janelia-experimental-technology/FED3-RFID/ELECTRONICS/PHOTOS/20240327_181024.jpg

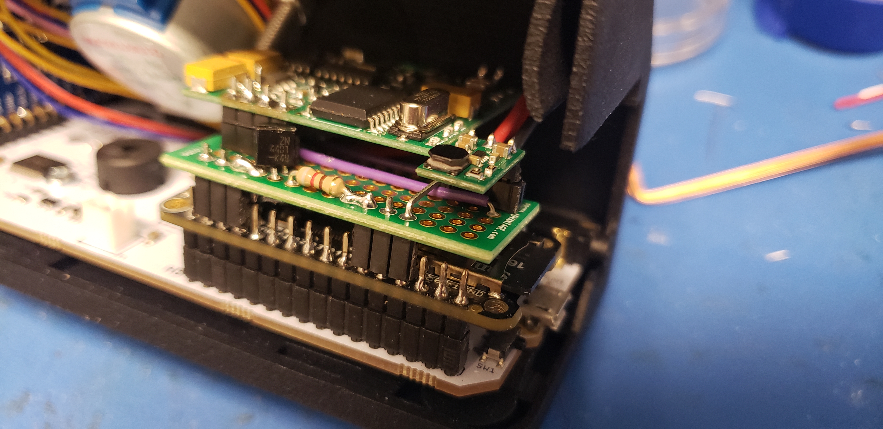
ELECTRONICS/PHOTOS/20240327_181024.jpg
