janelia-experimental-technology/FED3-RFID/ELECTRONICS/PHOTOS/20240327_181121.jpg

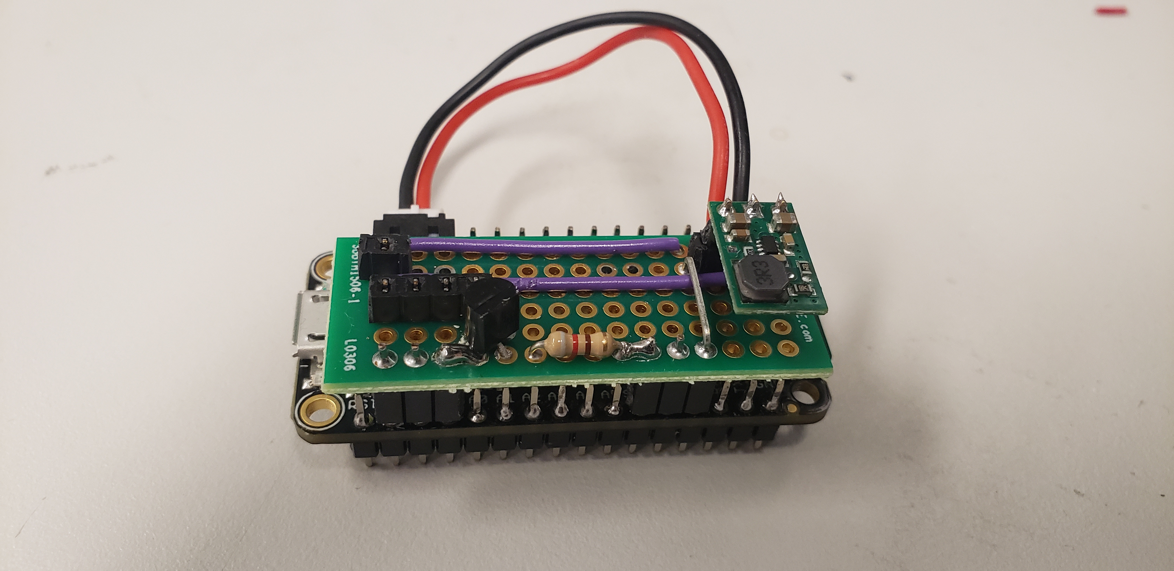
ELECTRONICS/PHOTOS/20240327_181121.jpg
