janelia-experimental-technology/FED3-RFID/FIRMWARE/FED3_support_libraries/Adafruit_AHTX0/assets/board.png

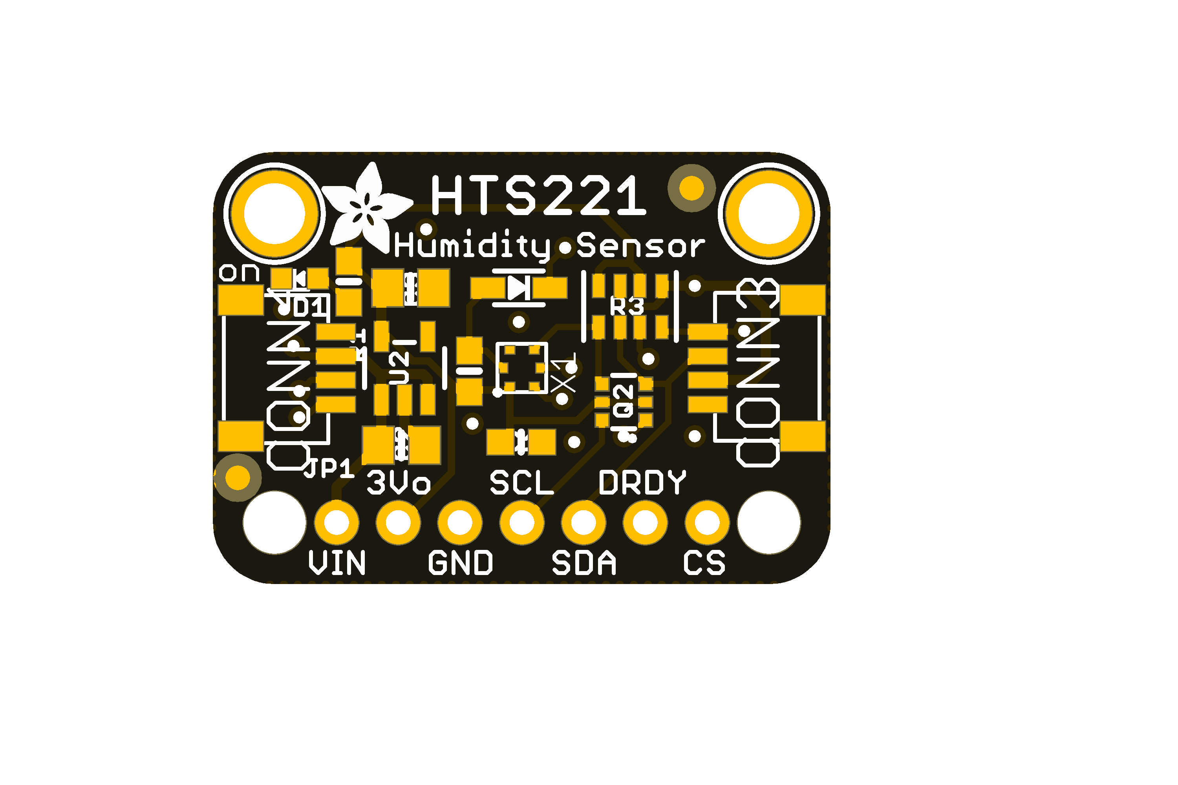
FIRMWARE/FED3_support_libraries/Adafruit_AHTX0/assets/board.png
