janelia-experimental-technology/FED3-RFID/FIRMWARE/FED3_support_libraries/SdFat/extras/AnalogBinLoggerExtras/ADC_ENOB.PNG

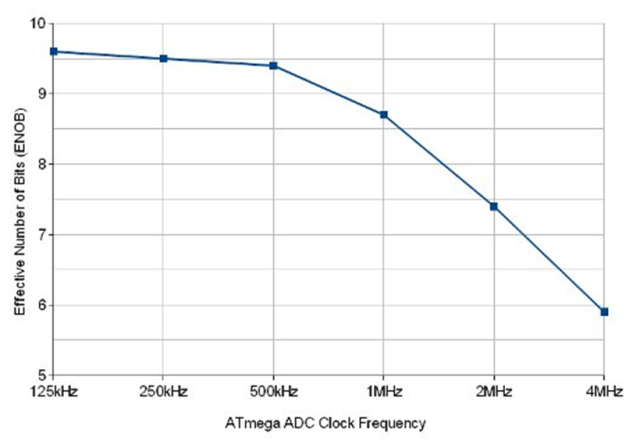
FIRMWARE/FED3_support_libraries/SdFat/extras/AnalogBinLoggerExtras/ADC_ENOB.PNG
