janelia-experimental-technology/FED3-RFID/FIRMWARE/FED3_support_libraries/SdFat/extras/AnalogBinLoggerExtras/DATA.png

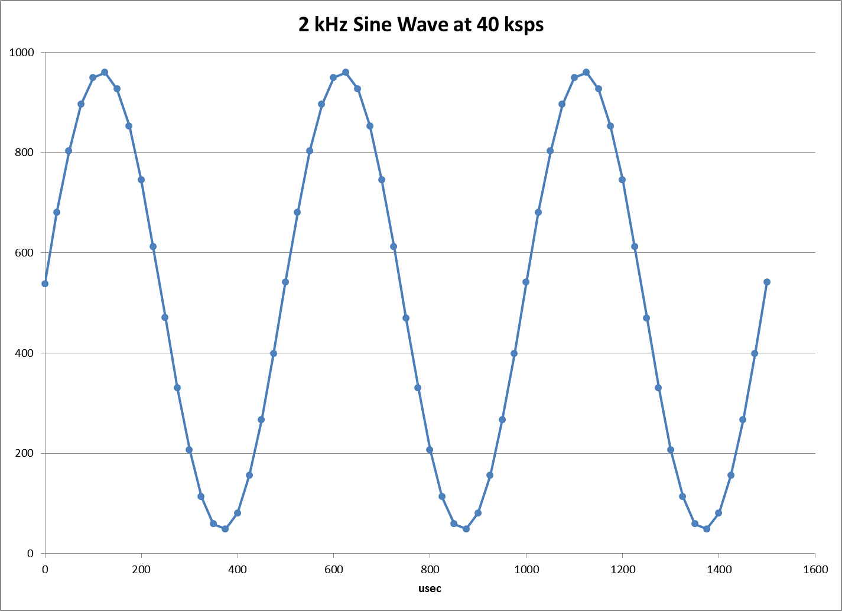
FIRMWARE/FED3_support_libraries/SdFat/extras/AnalogBinLoggerExtras/DATA.png
