janelia-experimental-technology/FED3-RFID/FIRMWARE/FED3_support_libraries/SdFat/extras/html/_fat_file_8h__incl.png

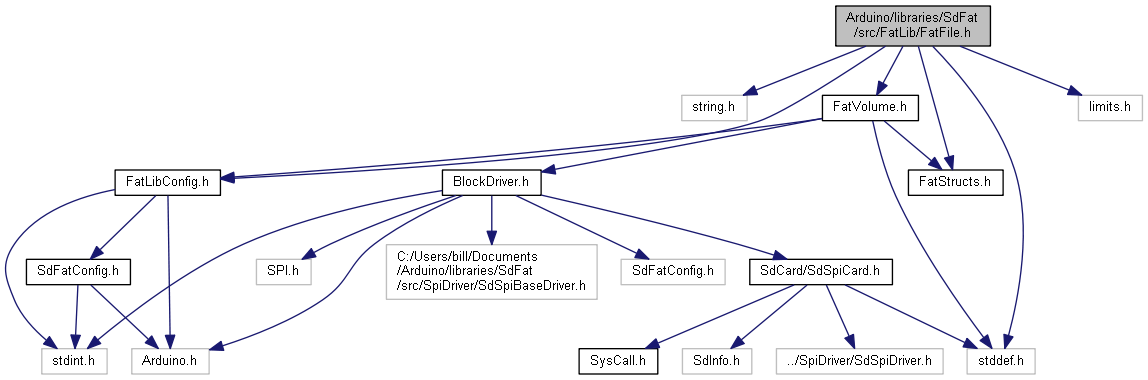
FIRMWARE/FED3_support_libraries/SdFat/extras/html/_fat_file_8h__incl.png
