janelia-experimental-technology/FED3-RFID/FIRMWARE/FED3_support_libraries/SdFat/extras/html/_sd_fat_8h__incl.png

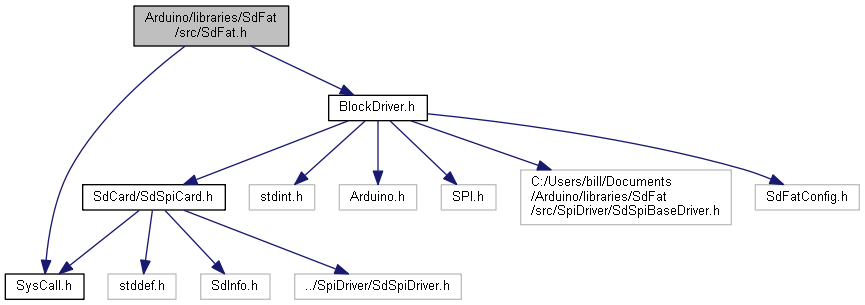
FIRMWARE/FED3_support_libraries/SdFat/extras/html/_sd_fat_8h__incl.png
