janelia-experimental-technology/FED3-RFID/FIRMWARE/FED3_support_libraries/SdFat/extras/html/_sys_call_8h__dep__incl.png

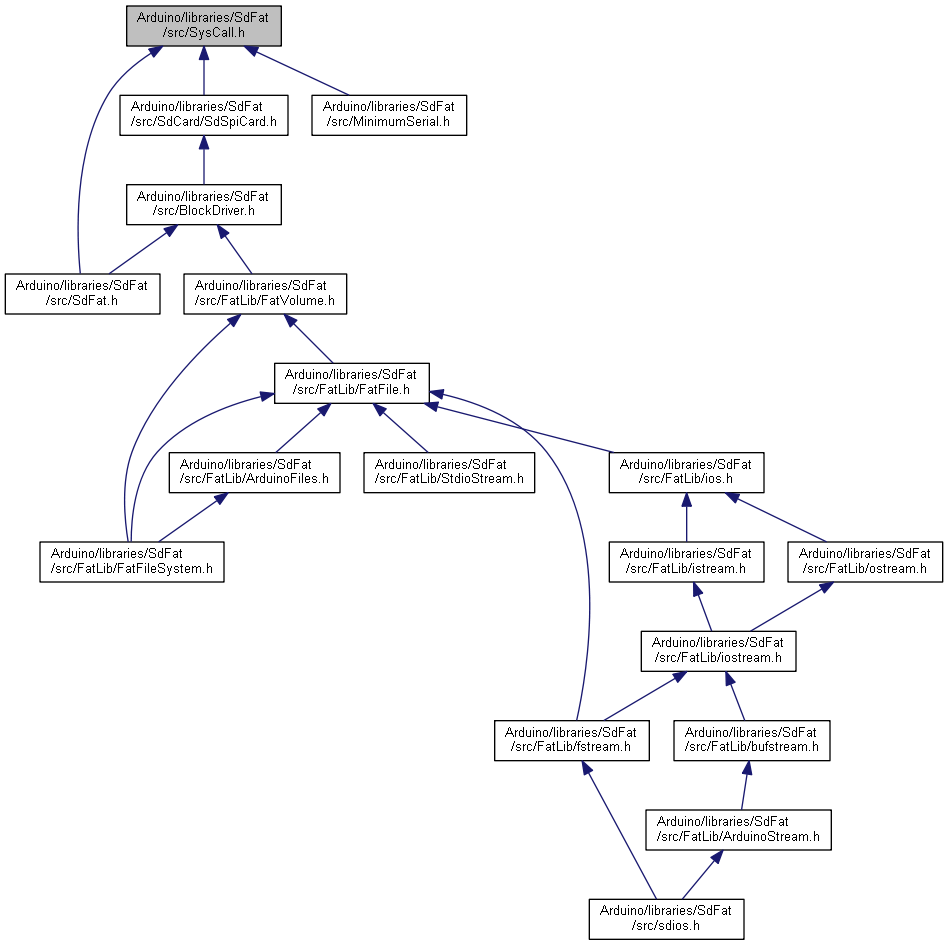
FIRMWARE/FED3_support_libraries/SdFat/extras/html/_sys_call_8h__dep__incl.png
