janelia-experimental-technology/FED3-RFID/FIRMWARE/FED3_support_libraries/SdFat/extras/html/class_arduino_in_stream__coll__graph.png

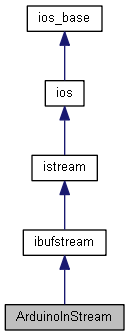
FIRMWARE/FED3_support_libraries/SdFat/extras/html/class_arduino_in_stream__coll__graph.png
