janelia-experimental-technology/FED3-RFID/FIRMWARE/FED3_support_libraries/SdFat/extras/html/class_base_block_driver__inherit__graph.png

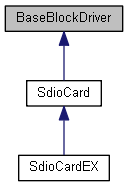
FIRMWARE/FED3_support_libraries/SdFat/extras/html/class_base_block_driver__inherit__graph.png
