janelia-experimental-technology/FED3-RFID/FIRMWARE/FED3_support_libraries/SdFat/extras/html/class_fat_file__inherit__graph.png

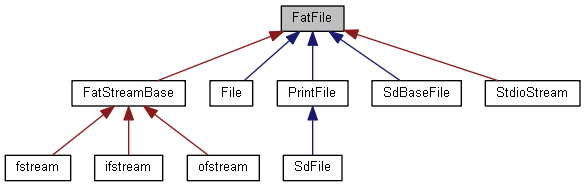
FIRMWARE/FED3_support_libraries/SdFat/extras/html/class_fat_file__inherit__graph.png
