janelia-experimental-technology/FED3-RFID/FIRMWARE/FED3_support_libraries/SdFat/extras/html/class_fat_stream_base__inherit__graph.png

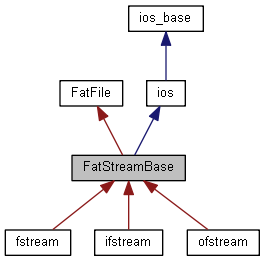
FIRMWARE/FED3_support_libraries/SdFat/extras/html/class_fat_stream_base__inherit__graph.png
