janelia-experimental-technology/FED3-RFID/FIRMWARE/FED3_support_libraries/SdFat/extras/html/class_sd_fat_sdio__coll__graph.png

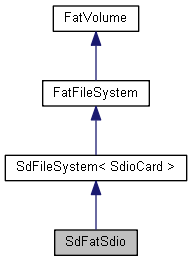
FIRMWARE/FED3_support_libraries/SdFat/extras/html/class_sd_fat_sdio__coll__graph.png
