janelia-experimental-technology/FED3-RFID/FIRMWARE/FED3_support_libraries/SdFat/extras/html/classfstream__coll__graph.png

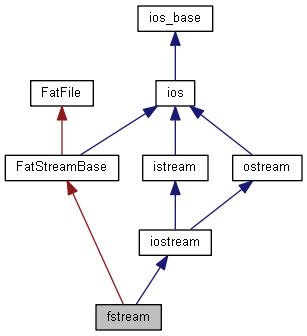
FIRMWARE/FED3_support_libraries/SdFat/extras/html/classfstream__coll__graph.png
