janelia-experimental-technology/FED3-RFID/FIRMWARE/FED3_support_libraries/SdFat/extras/html/dir_7e472674a7b7d2590a789f197241f95f_dep.png

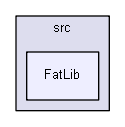
FIRMWARE/FED3_support_libraries/SdFat/extras/html/dir_7e472674a7b7d2590a789f197241f95f_dep.png
