janelia-experimental-technology/FED3-RFID/FIRMWARE/FED3_support_libraries/SdFat/extras/html/dir_481cc946b8a81b8d9363a4aad6201160_dep.png

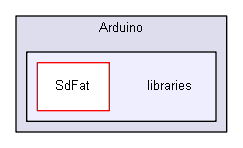
FIRMWARE/FED3_support_libraries/SdFat/extras/html/dir_481cc946b8a81b8d9363a4aad6201160_dep.png
