janelia-experimental-technology/FED3-RFID/FIRMWARE/FED3_support_libraries/SdFat/extras/html/dir_1281b15c327061056ab3b326e90c50cf_dep.png

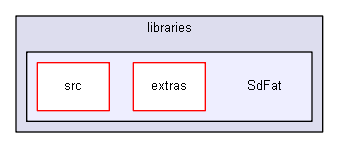
FIRMWARE/FED3_support_libraries/SdFat/extras/html/dir_1281b15c327061056ab3b326e90c50cf_dep.png
