janelia-experimental-technology/FED3-RFID/FIRMWARE/FED3_support_libraries/SdFat/extras/html/dir_c18d6c86f7b0afecac5c3a8a9885031e_dep.png

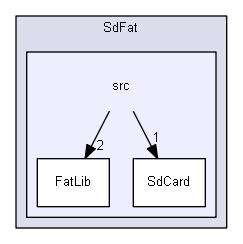
FIRMWARE/FED3_support_libraries/SdFat/extras/html/dir_c18d6c86f7b0afecac5c3a8a9885031e_dep.png
