janelia-experimental-technology/FED3-RFID/FIRMWARE/FED3_support_libraries/SdFat/extras/html/graph_legend.png

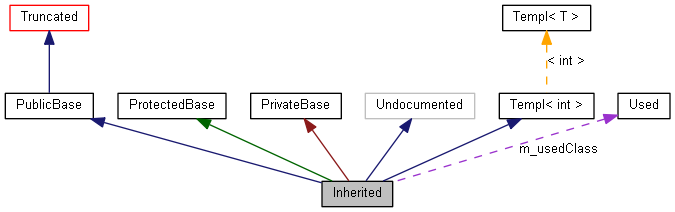
FIRMWARE/FED3_support_libraries/SdFat/extras/html/graph_legend.png
