janelia-experimental-technology/FED3-RFID/FIRMWARE/FED3_support_libraries/SdFat/extras/html/inherit_graph_10.png

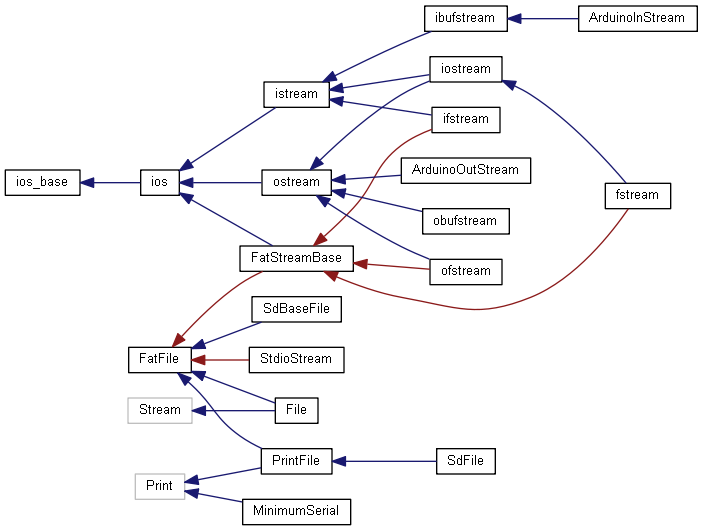
FIRMWARE/FED3_support_libraries/SdFat/extras/html/inherit_graph_10.png
