janelia-experimental-technology/FED3-RFID/FIRMWARE/FED3_support_libraries/SdFat/extras/html/structmaster_boot_record__coll__graph.png

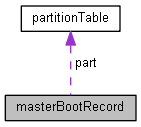
FIRMWARE/FED3_support_libraries/SdFat/extras/html/structmaster_boot_record__coll__graph.png
