janelia-experimental-technology/FED3-RFID/FIRMWARE/FED3_support_libraries/SdFat/extras/html/unioncache__t__coll__graph.png

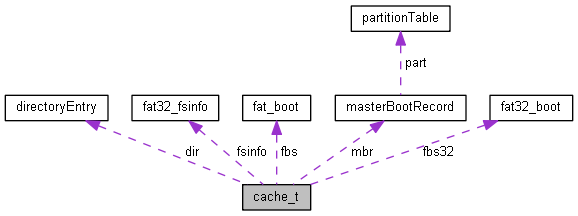
FIRMWARE/FED3_support_libraries/SdFat/extras/html/unioncache__t__coll__graph.png
