janelia-experimental-technology/FED3-RFID/RFID_HOUSING/PHOTOS/20240402_163826.jpg

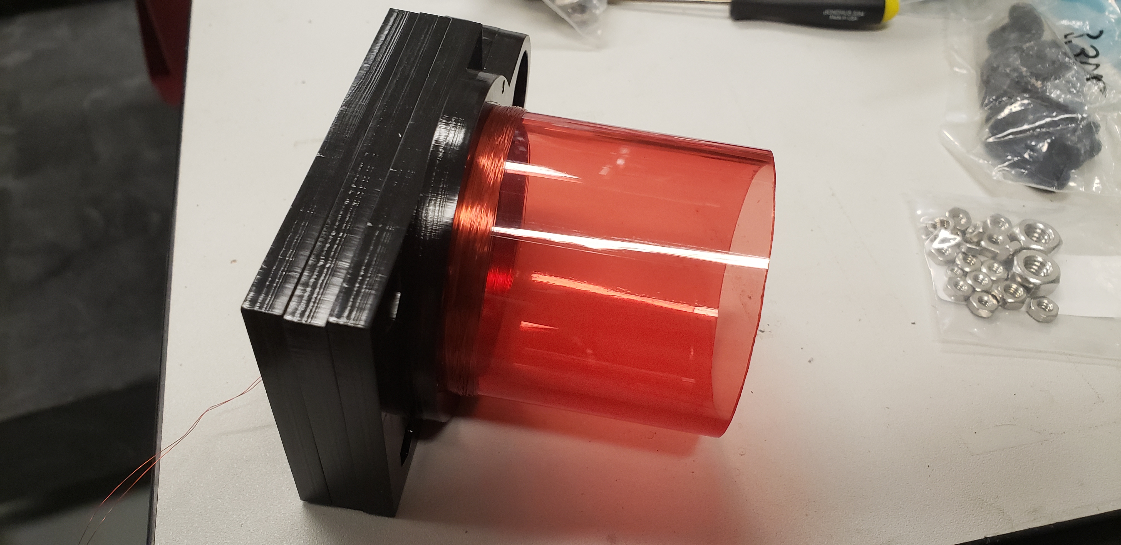
RFID_HOUSING/PHOTOS/20240402_163826.jpg
