janelia-experimental-technology/FED3-RFID/RFID_HOUSING/PHOTOS/20240402_172739.jpg

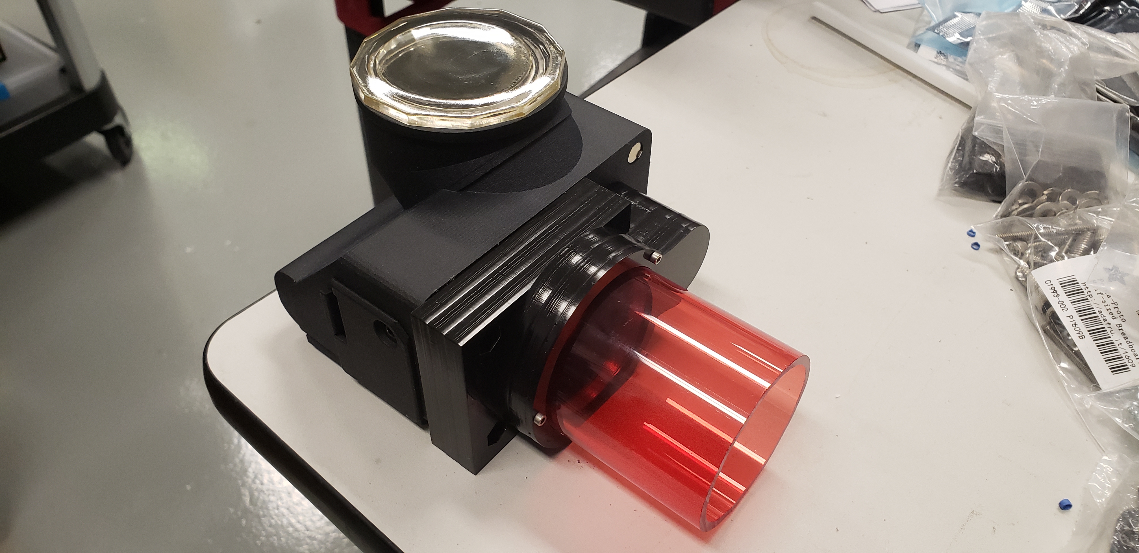
RFID_HOUSING/PHOTOS/20240402_172739.jpg
